shambhurajmane/Bionic-Arm/snaps/2.PNG

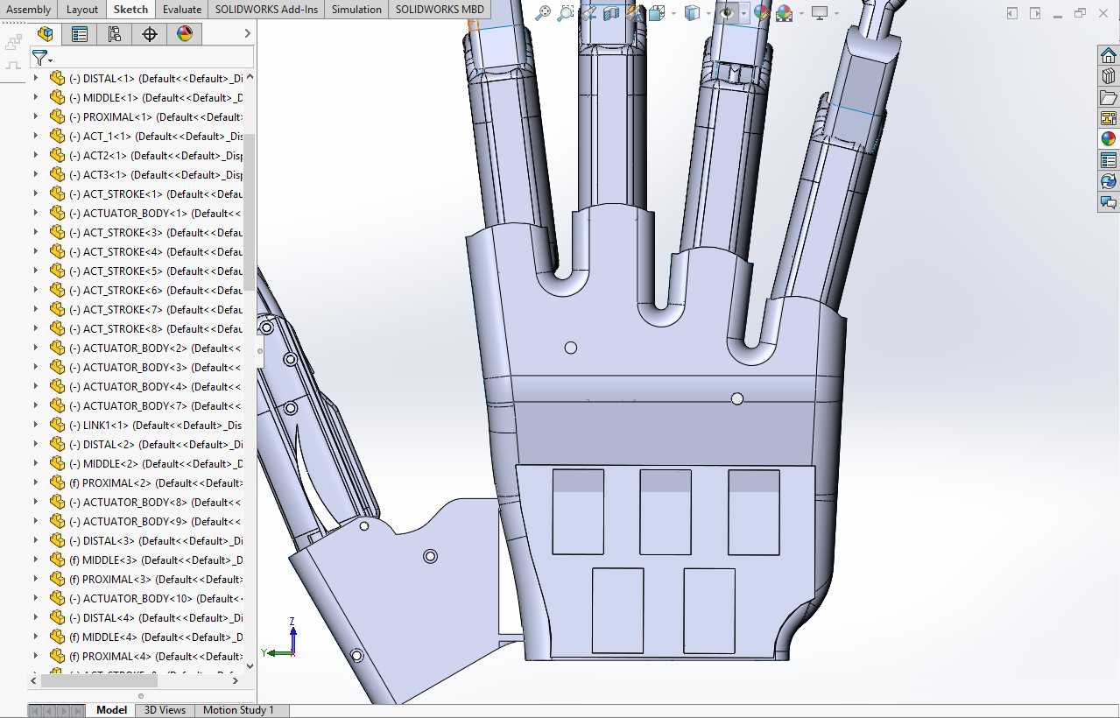
snaps/2.PNG
