shambhurajmane/Bionic-Arm/Reference Doc/WhatsApp Image 2020-09-21 at 2.15.28 PM.jpeg

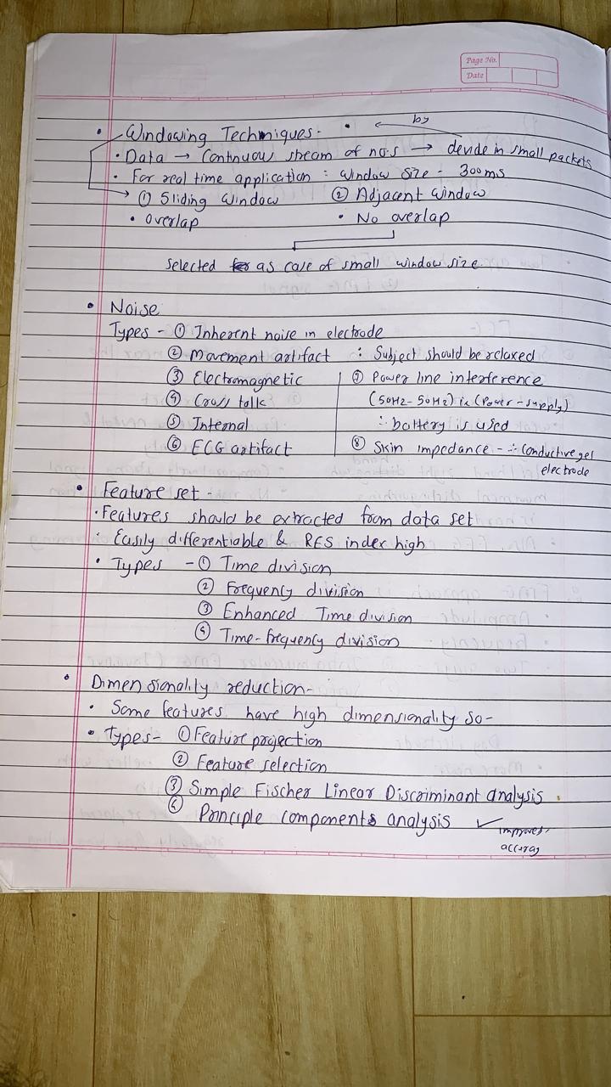
Reference Doc/WhatsApp Image 2020-09-21 at 2.15.28 PM.jpeg
