shambhurajmane/Bionic-Arm/Reference Doc/WhatsApp Image 2020-09-21 at 2.15.29 PM (1).jpeg

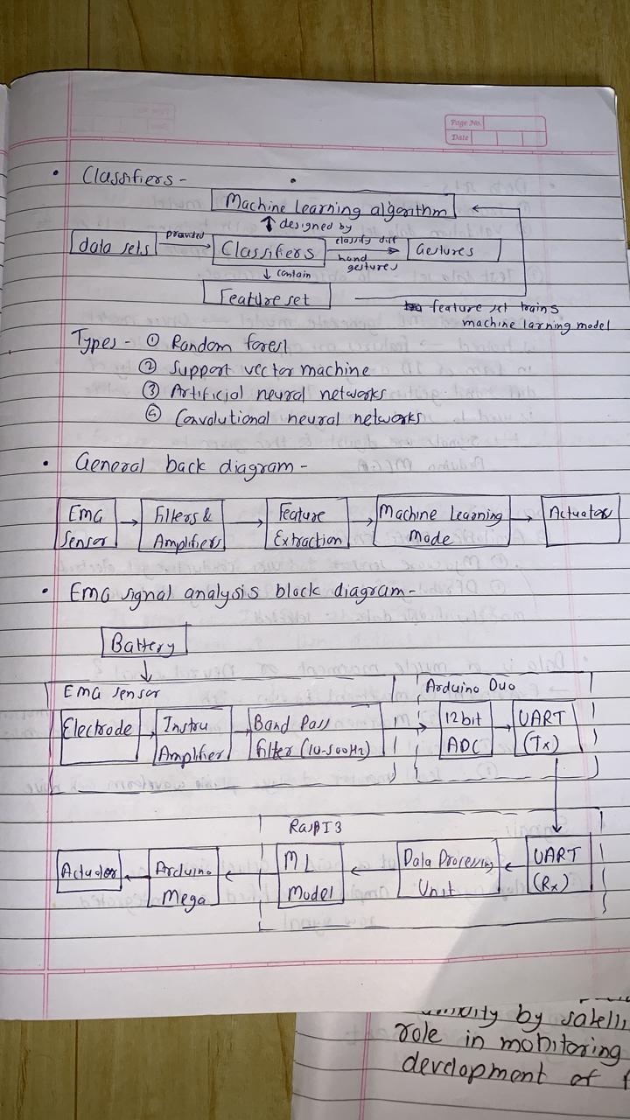
Reference Doc/WhatsApp Image 2020-09-21 at 2.15.29 PM (1).jpeg
