shambhurajmane/Bionic-Arm/snaps/1.PNG

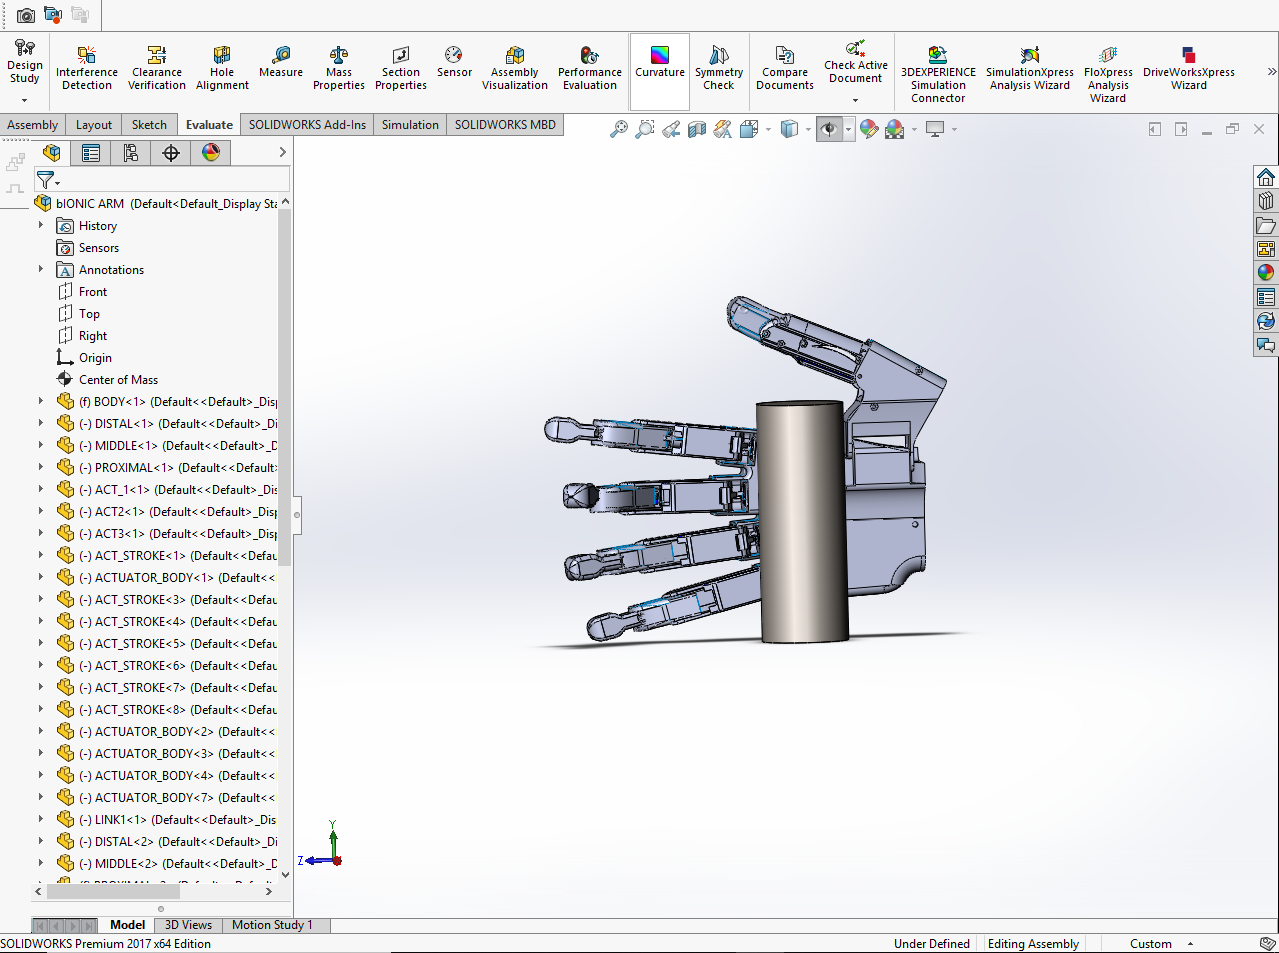
snaps/1.PNG
