shambhurajmane/Bionic-Arm/snaps/3.PNG

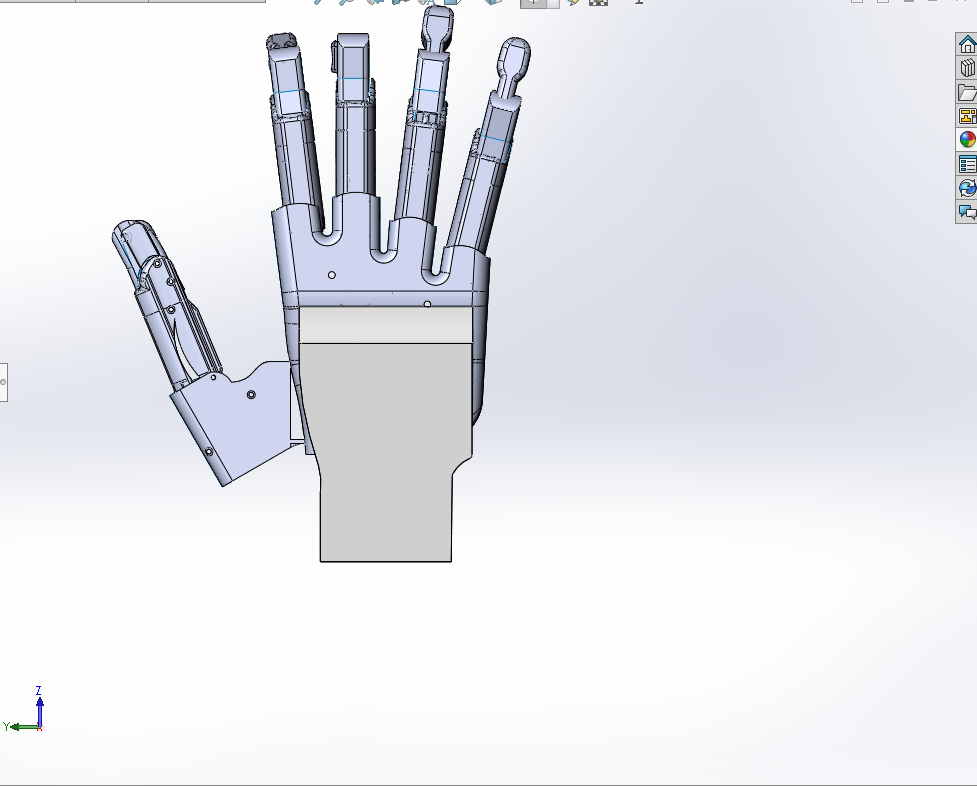
snaps/3.PNG
