shambhurajmane/Bionic-Arm/snaps/4.PNG

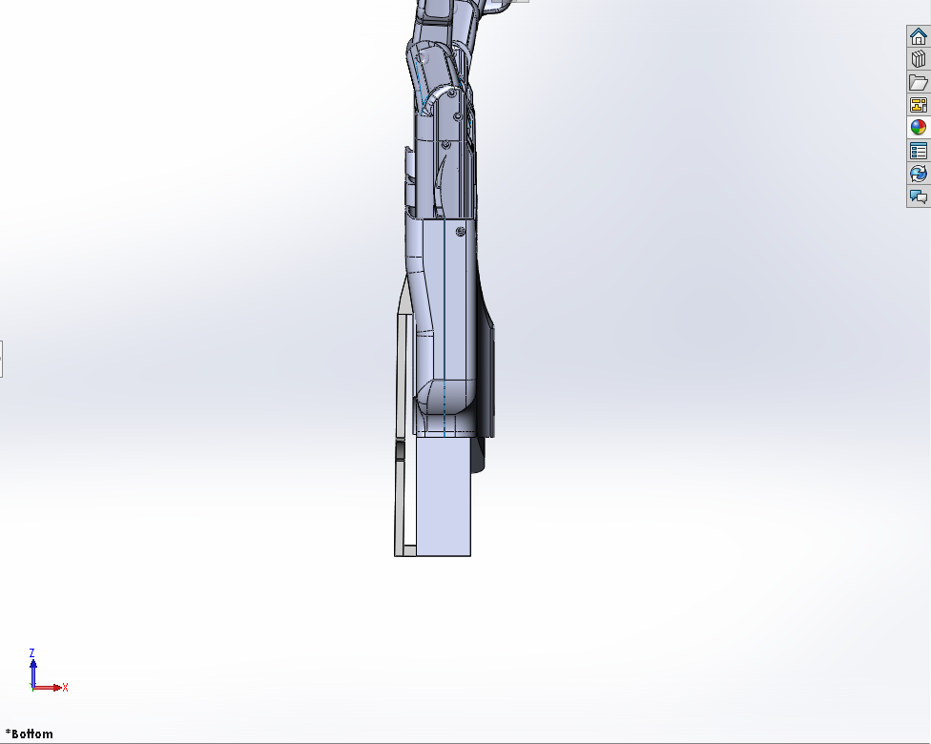
snaps/4.PNG
