shambhurajmane/Bionic-Arm/snaps/5.PNG

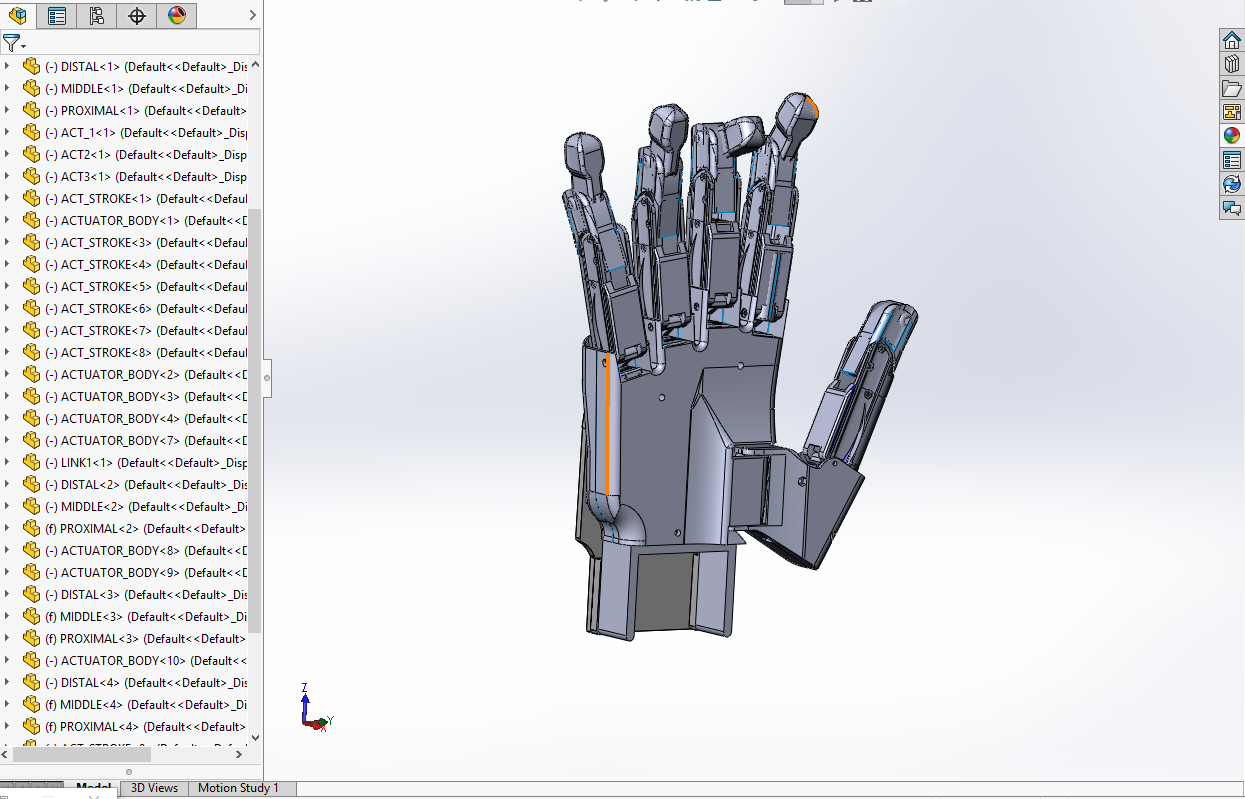
snaps/5.PNG
