shambhurajmane/Bionic-Arm/snaps/6.PNG

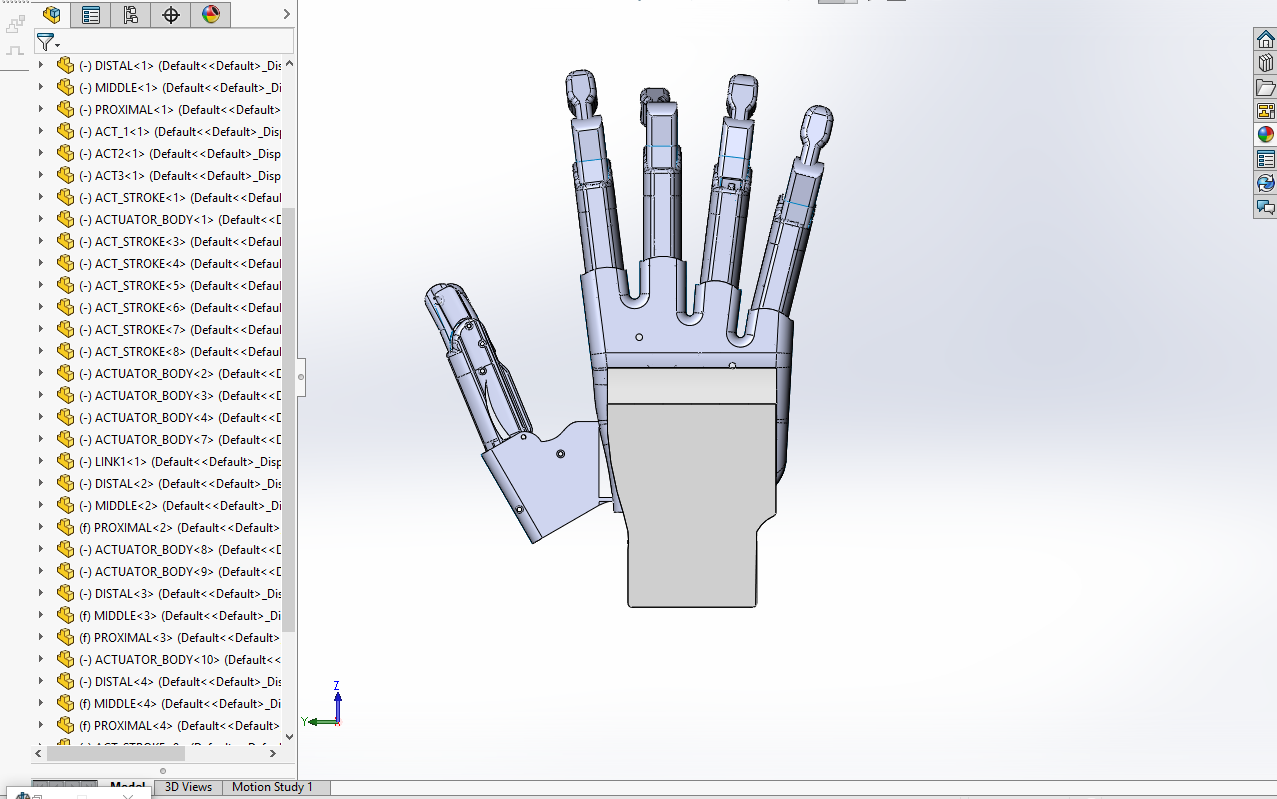
snaps/6.PNG
