shambhurajmane/Bionic-Arm/snaps/2019-07-16_16-17-27 (1).jpg

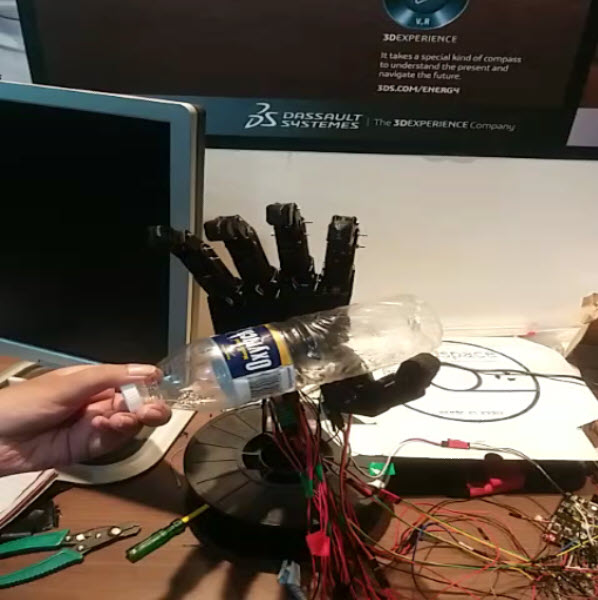
snaps/2019-07-16_16-17-27 (1).jpg
