shambhurajmane/Bionic-Arm/snaps/2019-07-16_16-18-21 (1).jpg

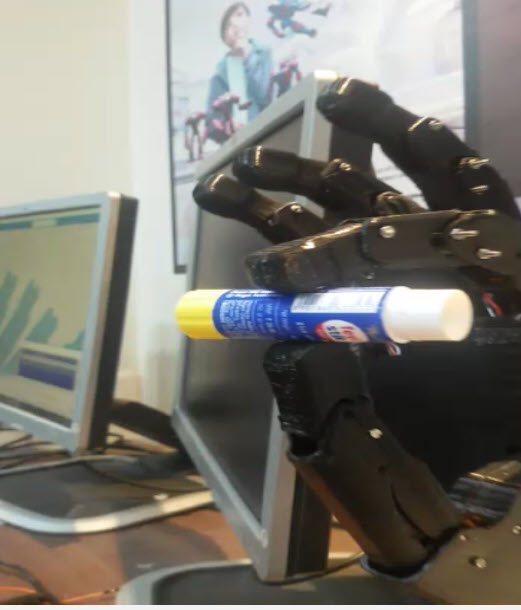
snaps/2019-07-16_16-18-21 (1).jpg
