shambhurajmane/Bionic-Arm/snaps/2019-07-16_16-19-02 (1).jpg

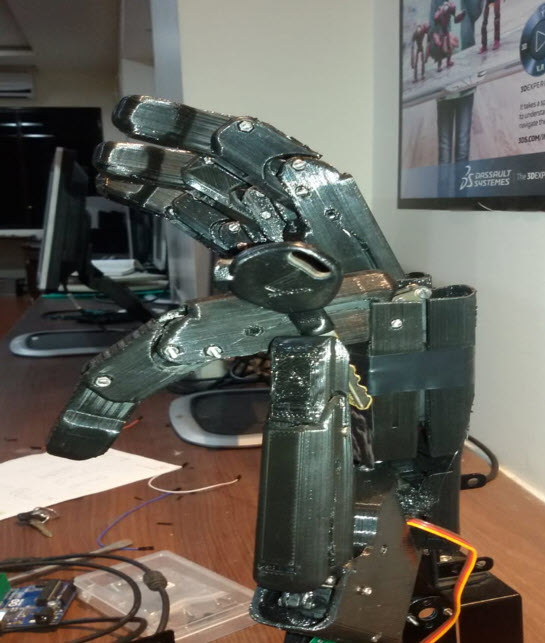
snaps/2019-07-16_16-19-02 (1).jpg
