shambhurajmane/Bionic-Arm/snaps/82905881_119986849751237_7641864399685935255_n.jpg

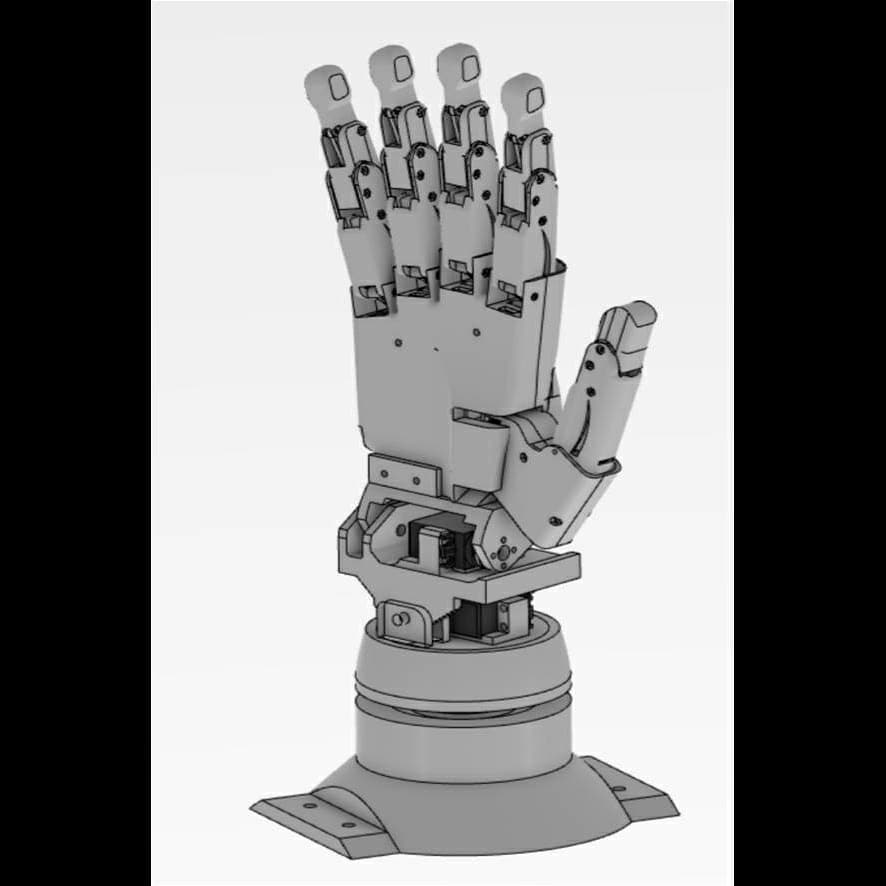
snaps/82905881_119986849751237_7641864399685935255_n.jpg
