shambhurajmane/Bionic-Arm/snaps/104155654_116260273222086_727207596559129069_n.jpg

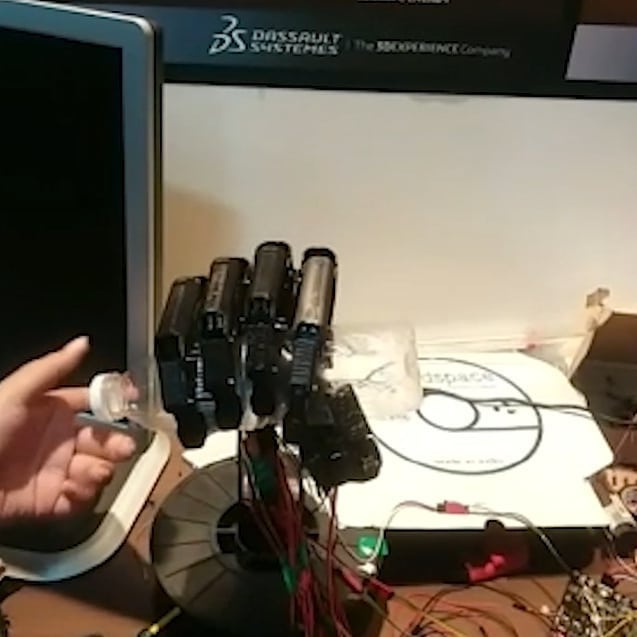
snaps/104155654_116260273222086_727207596559129069_n.jpg
