shambhurajmane/Bionic-Arm/snaps/104169575_311938133159158_3146879702113165955_n.jpg

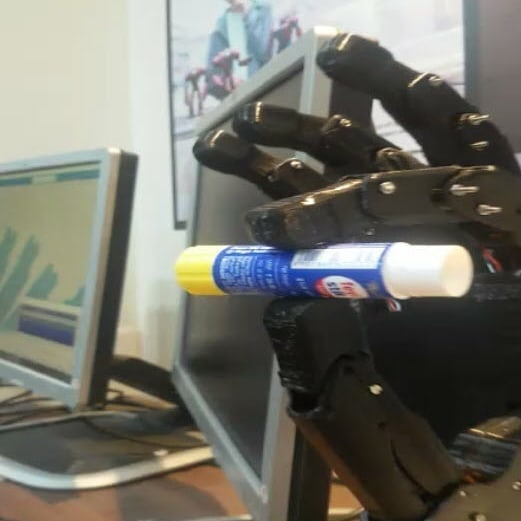
snaps/104169575_311938133159158_3146879702113165955_n.jpg
