shambhurajmane/Bionic-Arm/snaps/104484002_644796146248938_6983377368795708192_n.jpg

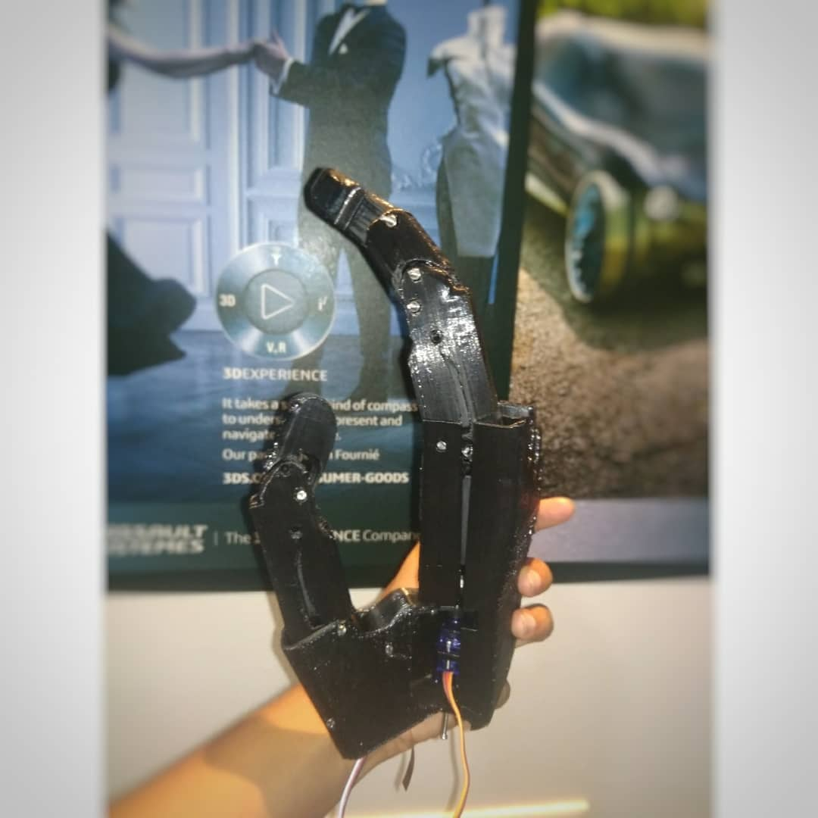
snaps/104484002_644796146248938_6983377368795708192_n.jpg
