shambhurajmane/Bionic-Arm/snaps/104968314_162162115284951_9102264236660171618_n.jpg

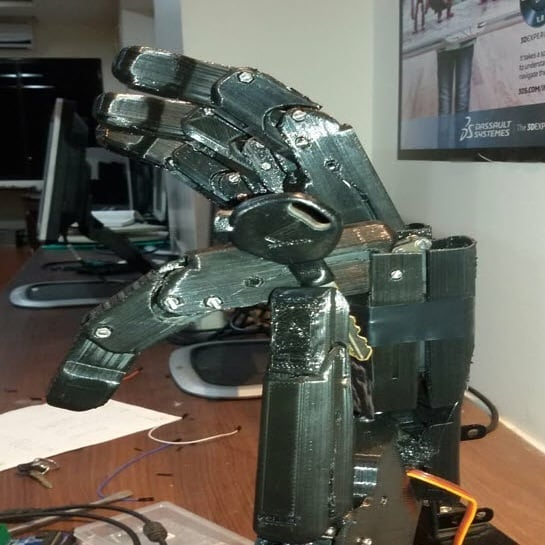
snaps/104968314_162162115284951_9102264236660171618_n.jpg
