shambhurajmane/Bionic-Arm/snaps/git1.png

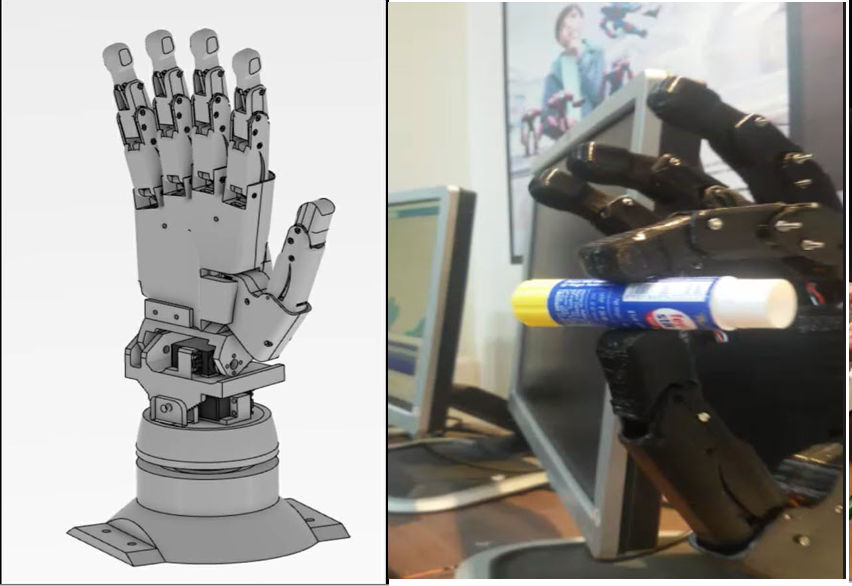
snaps/git1.png
