shambhurajmane/Bionic-Arm/snaps/WhatsApp Image 2020-12-11 at 12.13.05 PM.jpeg

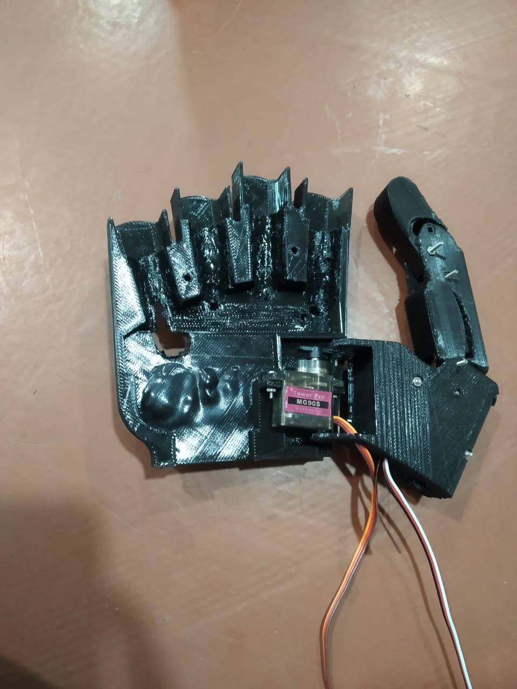
snaps/WhatsApp Image 2020-12-11 at 12.13.05 PM.jpeg
