shambhurajmane/Bionic-Arm/snaps/WhatsApp Image 2020-12-13 at 8.25.47 PM.jpeg

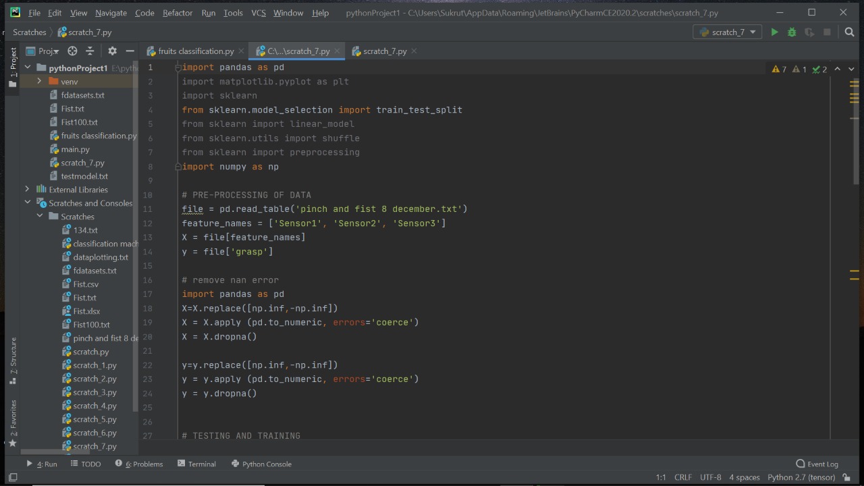
snaps/WhatsApp Image 2020-12-13 at 8.25.47 PM.jpeg
