shambhurajmane/Bionic-Arm/snaps/WhatsApp Image 2020-12-13 at 8.25.53 PM (1).jpeg

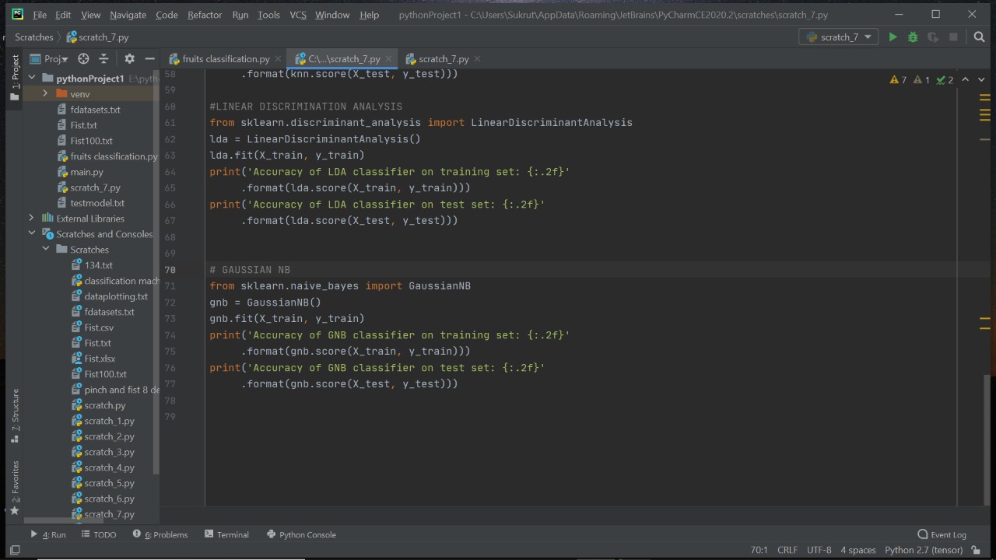
snaps/WhatsApp Image 2020-12-13 at 8.25.53 PM (1).jpeg
