shambhurajmane/Bionic-Arm/study_doc/applsci-07-01163-ag-550.jpg

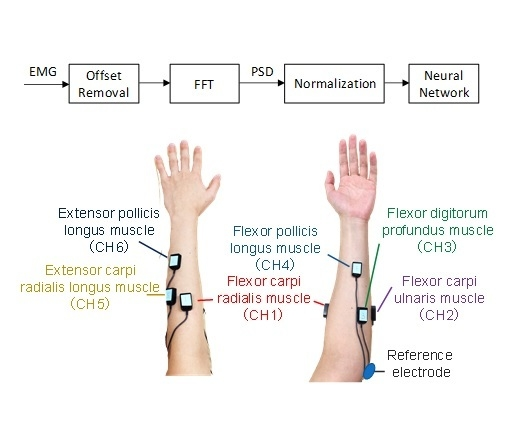
study_doc/applsci-07-01163-ag-550.jpg
