shambhurajmane/Bionic-Arm/study_doc/EMG_signal_decomposition.png

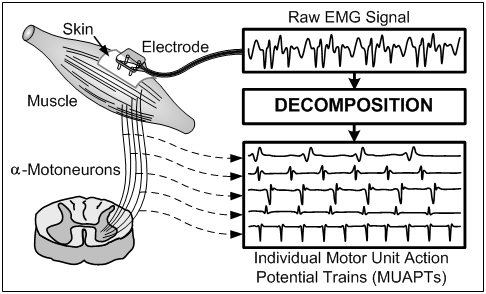
study_doc/EMG_signal_decomposition.png
