shambhurajmane/Bionic-Arm/study_doc/Figure2-ChangeInResistance.jpg

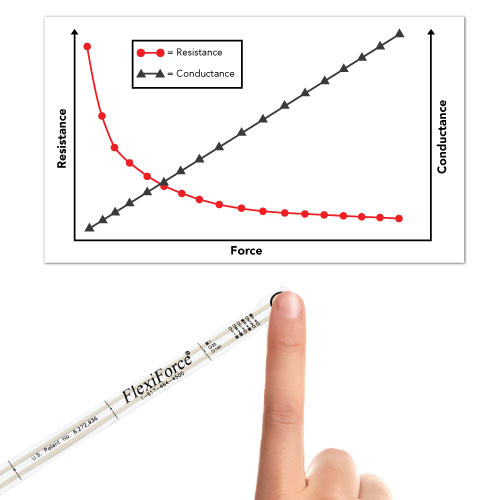
study_doc/Figure2-ChangeInResistance.jpg
