shambhurajmane/Bionic-Arm/study_doc/Force-Sensing-Resistor.jpg

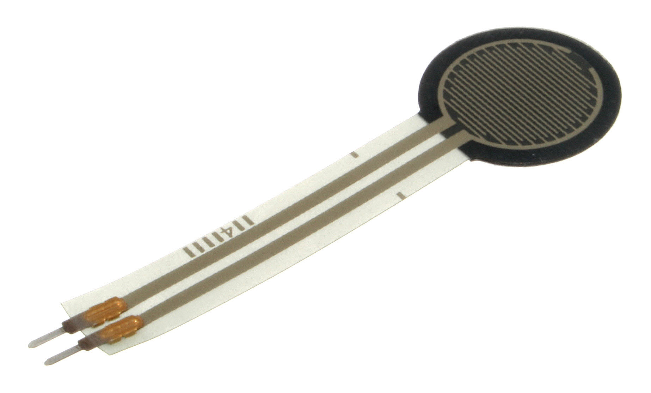
study_doc/Force-Sensing-Resistor.jpg
