shambhurajmane/Bionic-Arm/PARTS_SOLIDWORKS/ACT_STROKE.SLDPRT

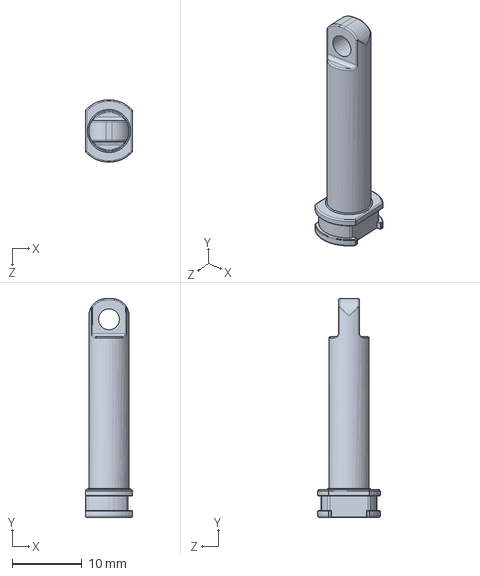
[picture p131: CAD file, 2022-11-02]
PARTS_SOLIDWORKS/ACT_STROKE.SLDPRT
6.80 x 31.5 x 9.00 mm
