shambhurajmane/Bionic-Arm/PARTS_SOLIDWORKS/BODY.SLDPRT

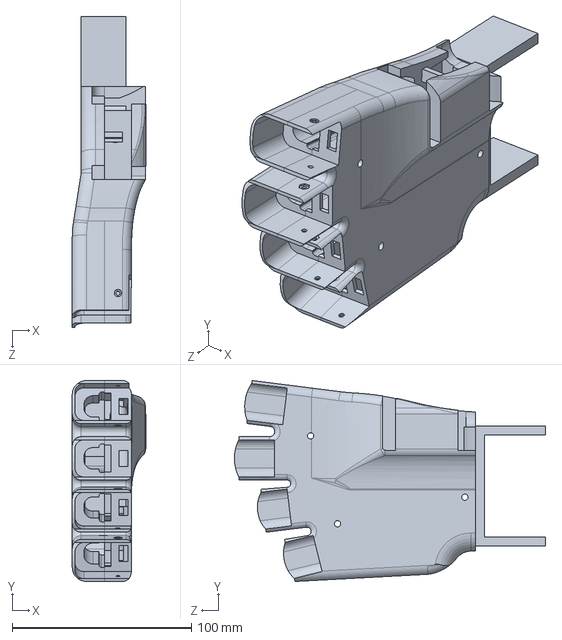
[picture p132: CAD file, 2022-11-02]
PARTS_SOLIDWORKS/BODY.SLDPRT
41.0 x 112.1 x 173.4 mm
