shambhurajmane/Bionic-Arm/PARTS_SOLIDWORKS/THUMB_BASE.SLDPRT

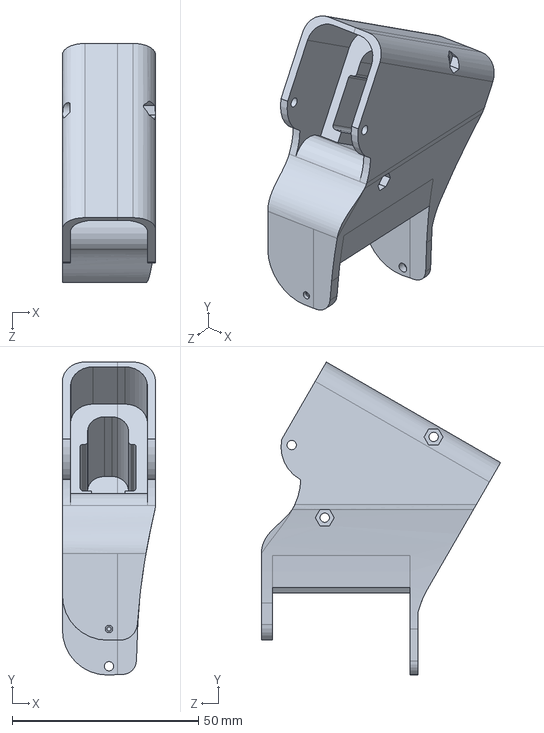
[picture p133: CAD file, 2022-11-02]
PARTS_SOLIDWORKS/THUMB_BASE.SLDPRT
25.0 x 84.0 x 64.2 mm
