shambhurajmane/Bionic-Arm/PARTS_SOLIDWORKS/ACT_1.SLDPRT

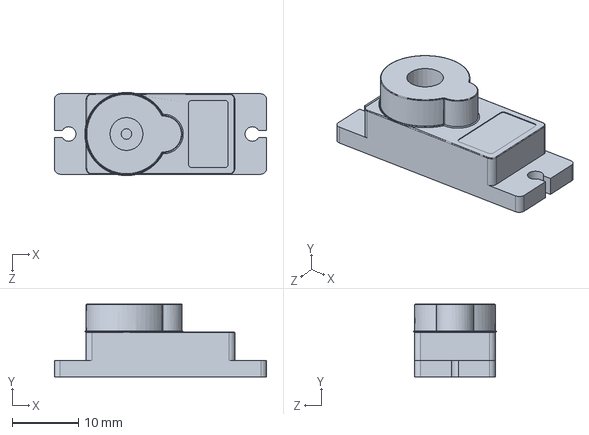
[picture p134: CAD file, 2022-11-02]
PARTS_SOLIDWORKS/ACT_1.SLDPRT
32.1 x 11.1 x 12.6 mm
