shambhurajmane/Bionic-Arm/PARTS_SOLIDWORKS/ACTUATOR_BODY.SLDPRT

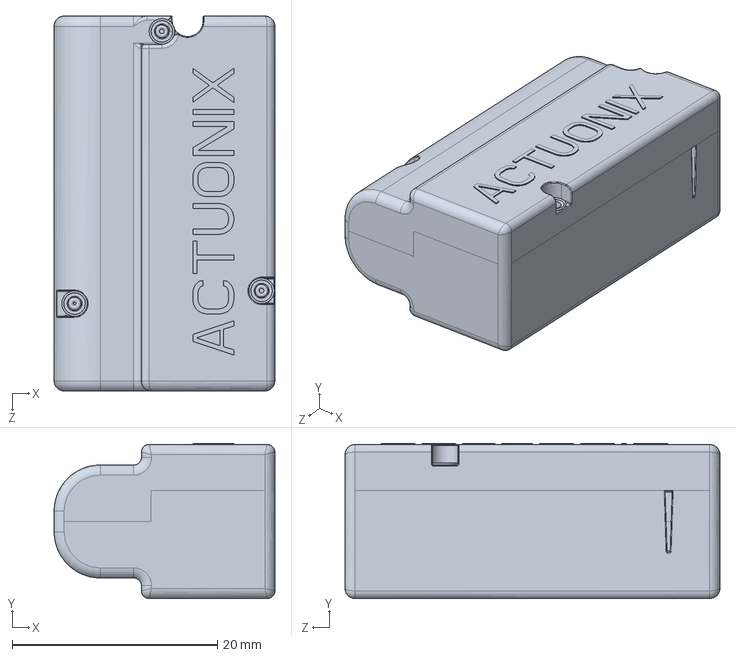
[picture p135: CAD file, 2022-11-02]
PARTS_SOLIDWORKS/ACTUATOR_BODY.SLDPRT
21.5 x 15.1 x 36.5 mm
