shambhurajmane/Bionic-Arm/PARTS_SOLIDWORKS/MIDDLE.SLDPRT

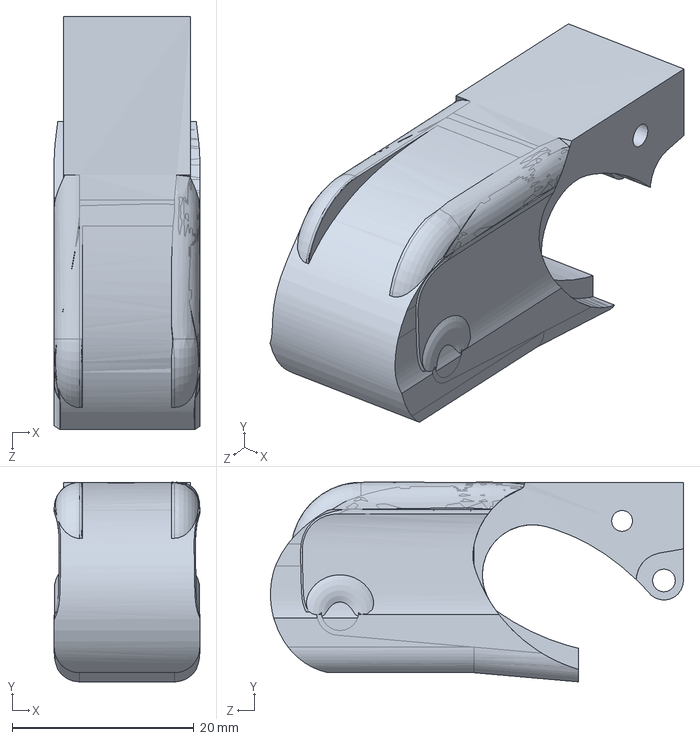
[picture p136: CAD file, 2022-11-02]
PARTS_SOLIDWORKS/MIDDLE.SLDPRT
16.0 x 22.0 x 45.4 mm
