shambhurajmane/Bionic-Arm/PARTS_SOLIDWORKS/LINK2.SLDPRT

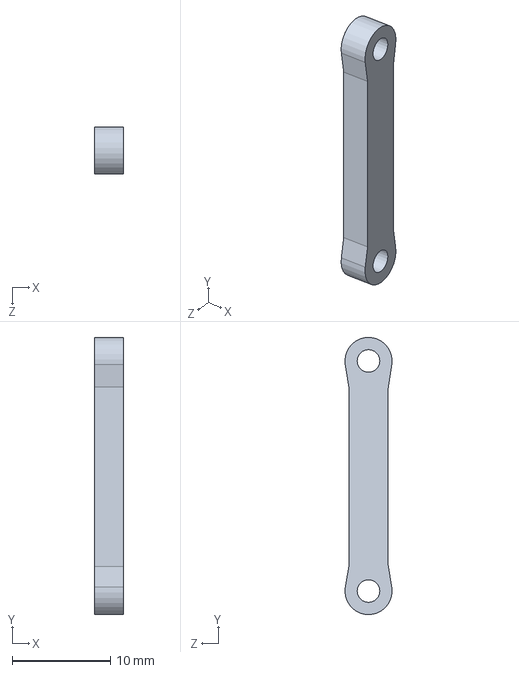
[picture p137: CAD file, 2022-11-02]
PARTS_SOLIDWORKS/LINK2.SLDPRT
2.90 x 28.2 x 4.79 mm
