shambhurajmane/Bionic-Arm/PARTS_SOLIDWORKS/TRIAL2.SLDPRT

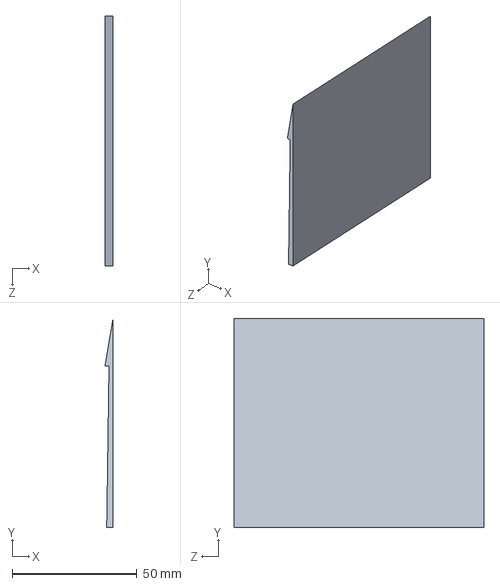
[picture p138: CAD file, 2022-11-02]
PARTS_SOLIDWORKS/TRIAL2.SLDPRT
3.22 x 83.6 x 100.0 mm
