shambhurajmane/Bionic-Arm/PARTS_SOLIDWORKS/TRIAL 3.SLDPRT

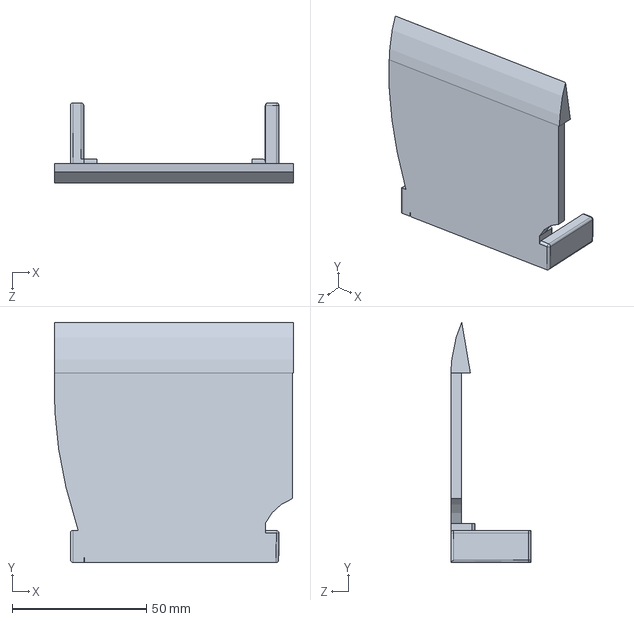
[picture p139: CAD file, 2022-11-02]
PARTS_SOLIDWORKS/TRIAL 3.SLDPRT
89.1 x 89.6 x 30.0 mm
