shambhurajmane/Bionic-Arm/code/arduino/basic/actuator_without_servo_fn/actuator_without_servo_fn.ino

int pwm =9;  // pwm [pin 
int angle=200;   //75 to 250


void setup() {
  pinMode(pwm,OUTPUT); 


 
  
}

void loop() {
  
                               
     
    if( angle <200)    
  {                                
    analogWrite(pwm,angle);  
    angle++;        
    delay(15);       
  }              


}
